bkpsu/KubeSensor/images/Kube-Base.png

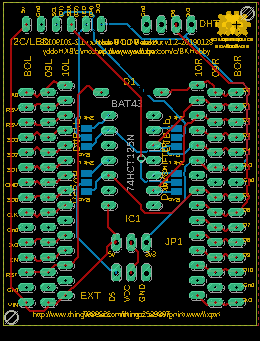
images/Kube-Base.png
