bkpsu/KubeSensor/images/Kube-Module-ADIO.png

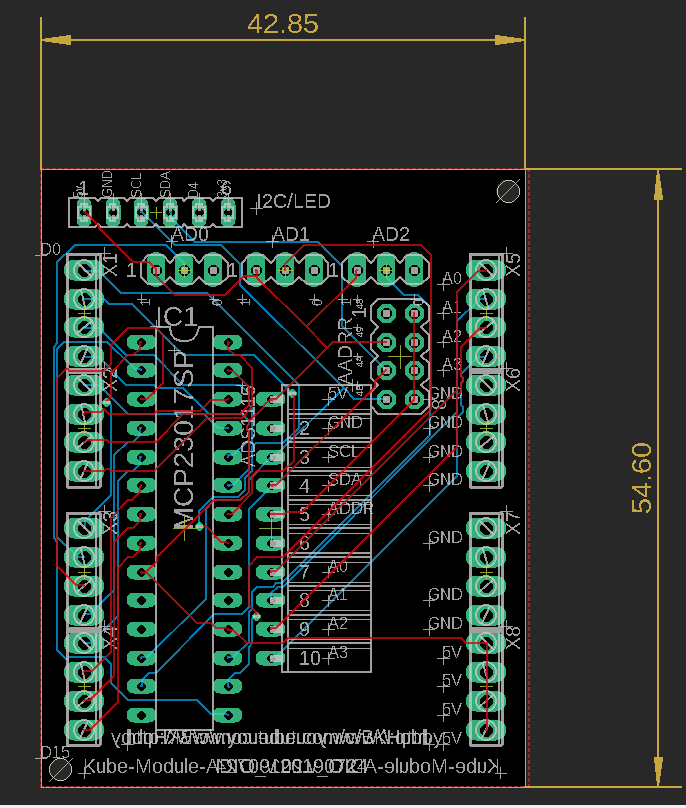
images/Kube-Module-ADIO.png
