bkpsu/KubeSensor/images/Kube-Module-OLED.png

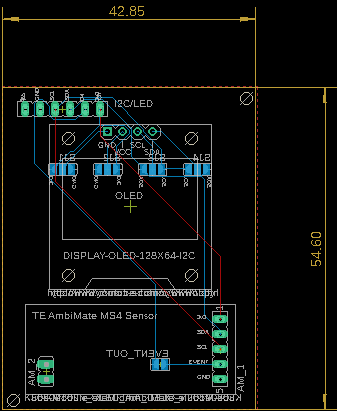
images/Kube-Module-OLED.png
