bkpsu/KubeSensor/images/Kube-Module-PS.png

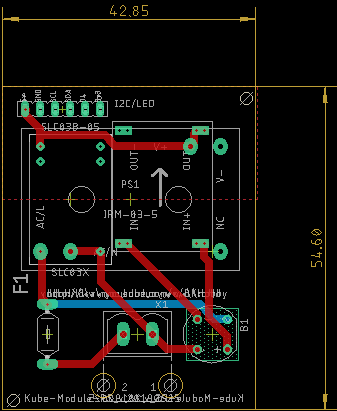
images/Kube-Module-PS.png
