bkpsu/KubeSensor/images/Kube-Module-Stack.png

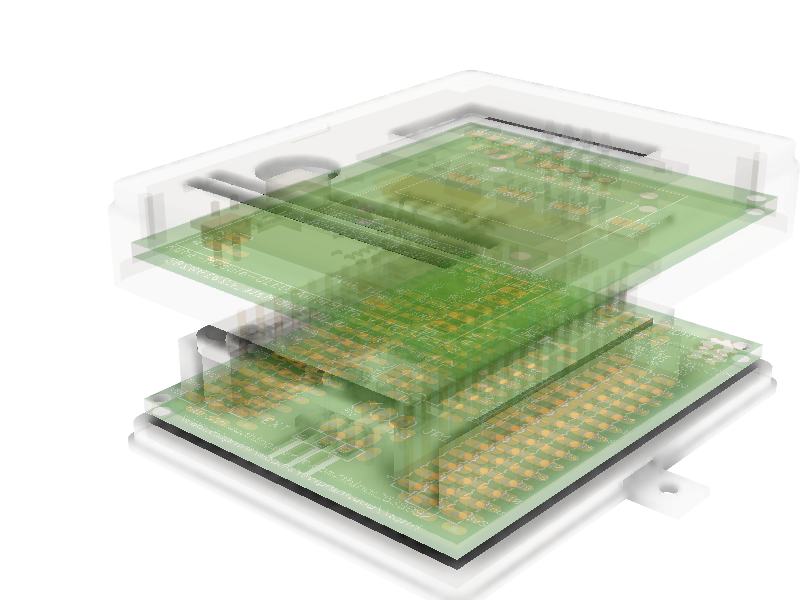
images/Kube-Module-Stack.png
