bkpsu/KubeSensor/images/Kube.jpg

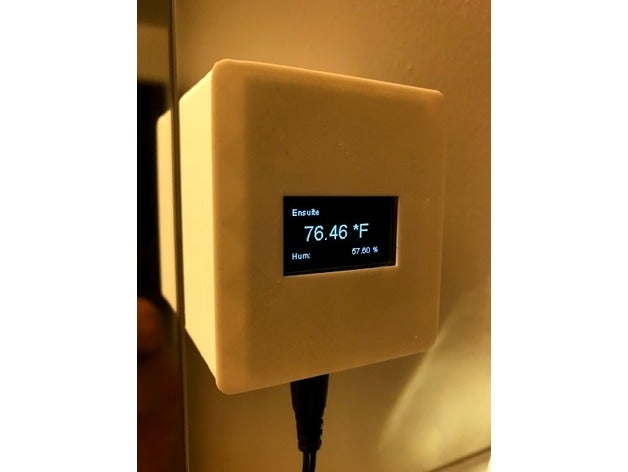
images/Kube.jpg
