bkpsu/KubeSensor/images/kubev2-adio-bottom.png

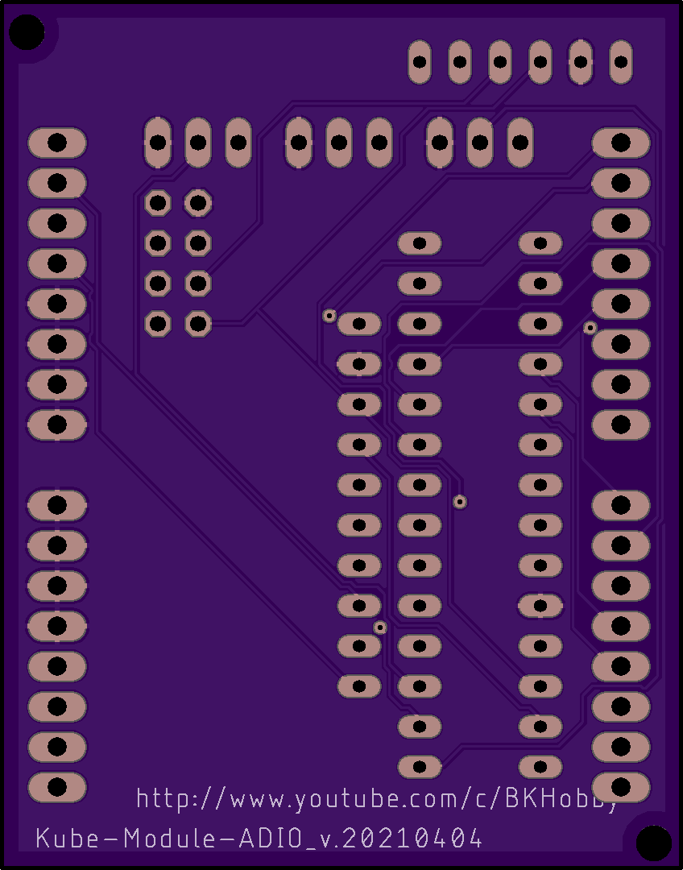
images/kubev2-adio-bottom.png
