bkpsu/KubeSensor/images/kubev2-helteclorav2-top.png

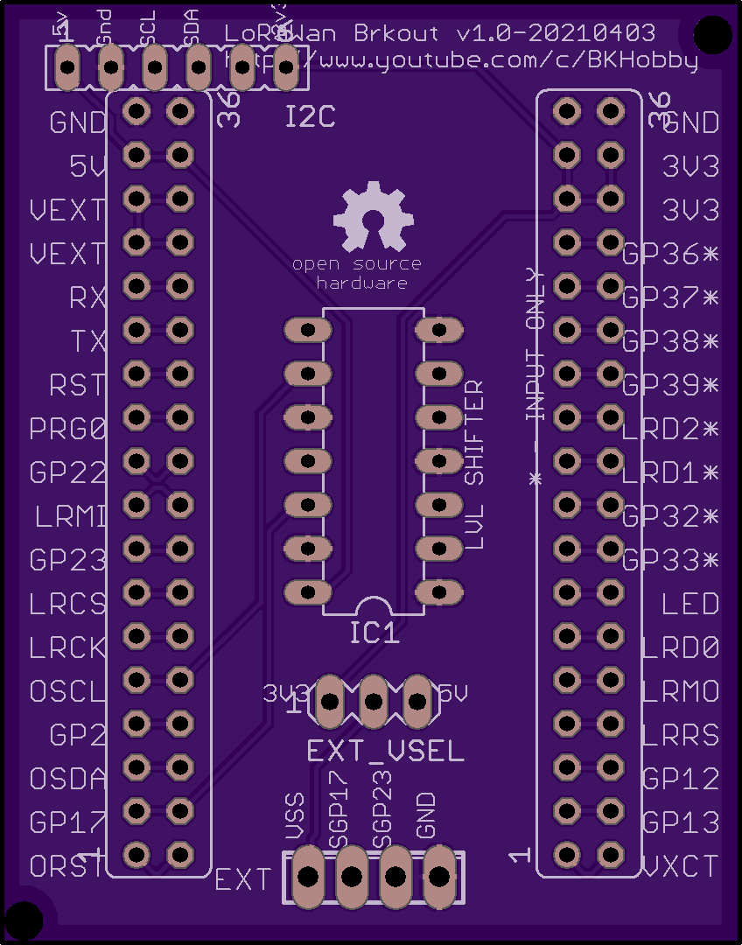
images/kubev2-helteclorav2-top.png
