bkpsu/KubeSensor/images/kubev2-nodemcu3d.png

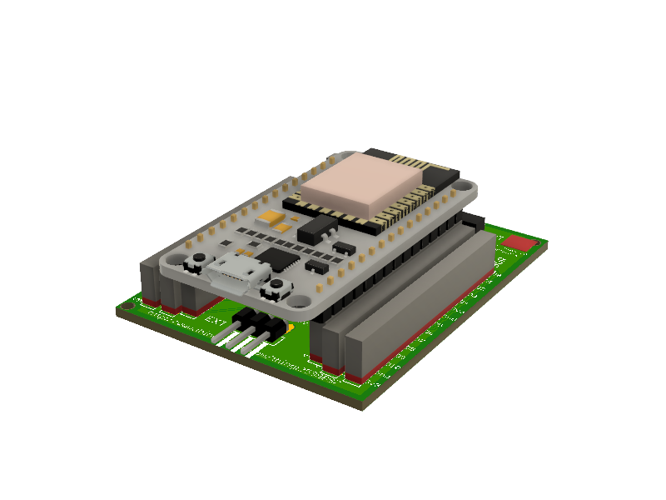
images/kubev2-nodemcu3d.png
