bkpsu/KubeSensor/images/Sideview.jpg

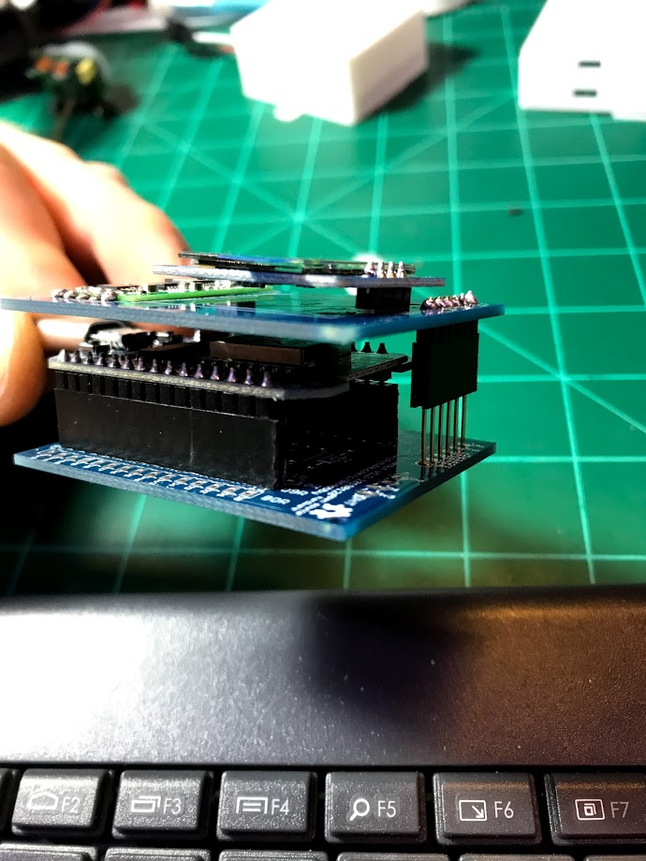
images/Sideview.jpg
