bkpsu/KubeSensor/images/values.jpg

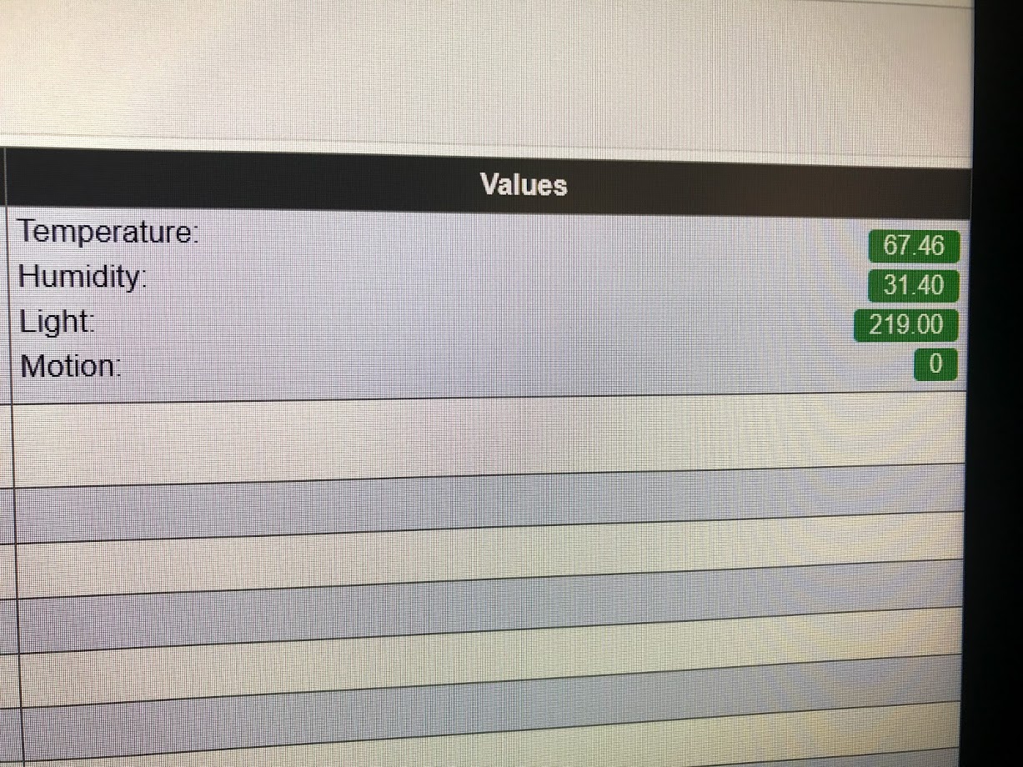
images/values.jpg
